ROHMUSDC/ROHMSensorPlatformEVK/Documentation/CE Declaration of Conformity/EUDC-DoC-201501-SENSEKIT2-EVK-101.pdf

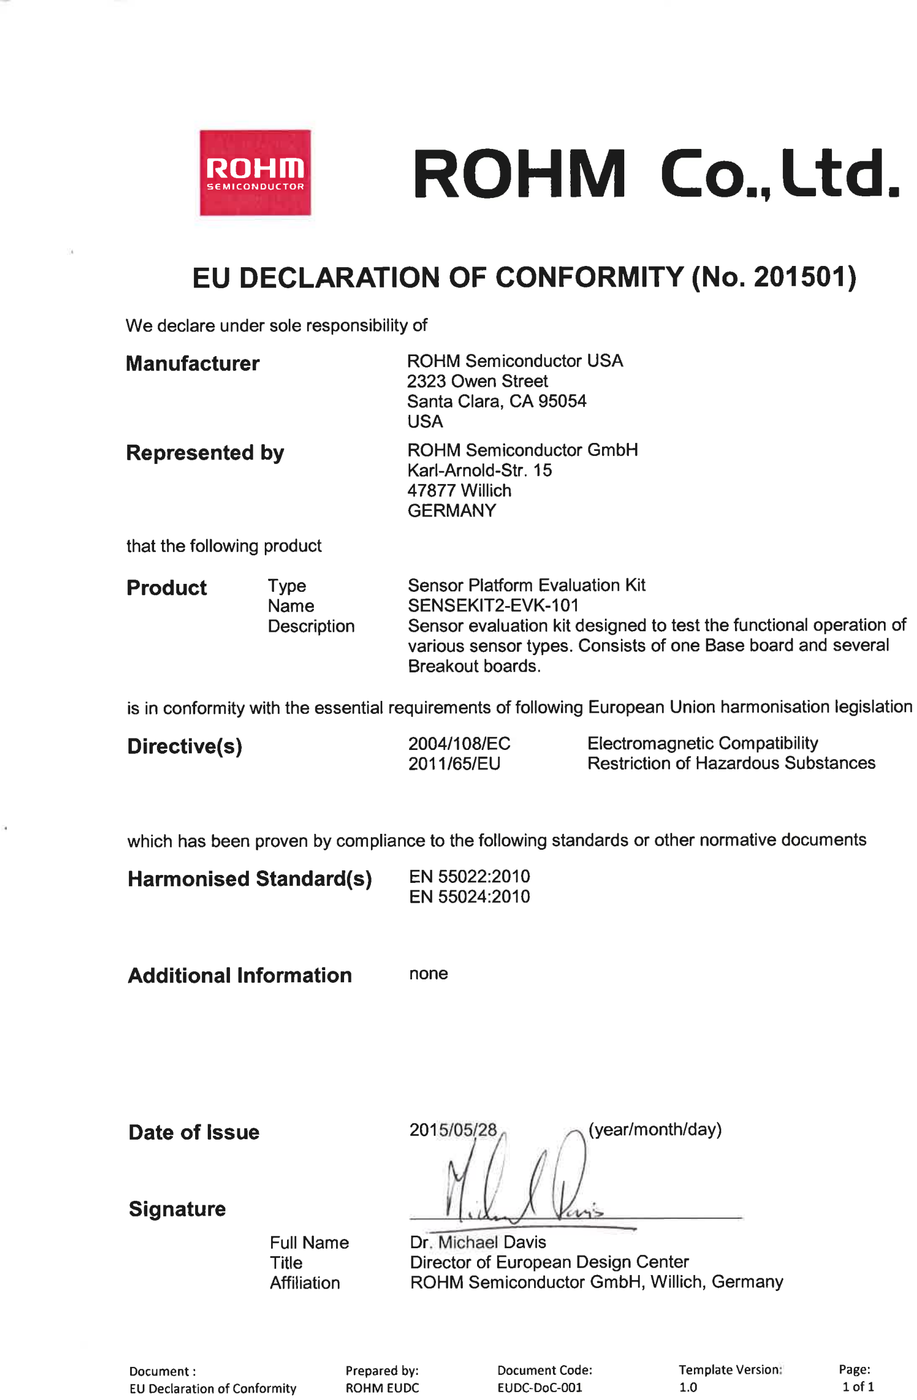
[picture p3: page 1]
