ROHMUSDC/ROHMSensorPlatformEVK/Documentation/CE Declaration of Conformity/technical_documentation/[14]_Photos/IMG_20150430_091738.jpg

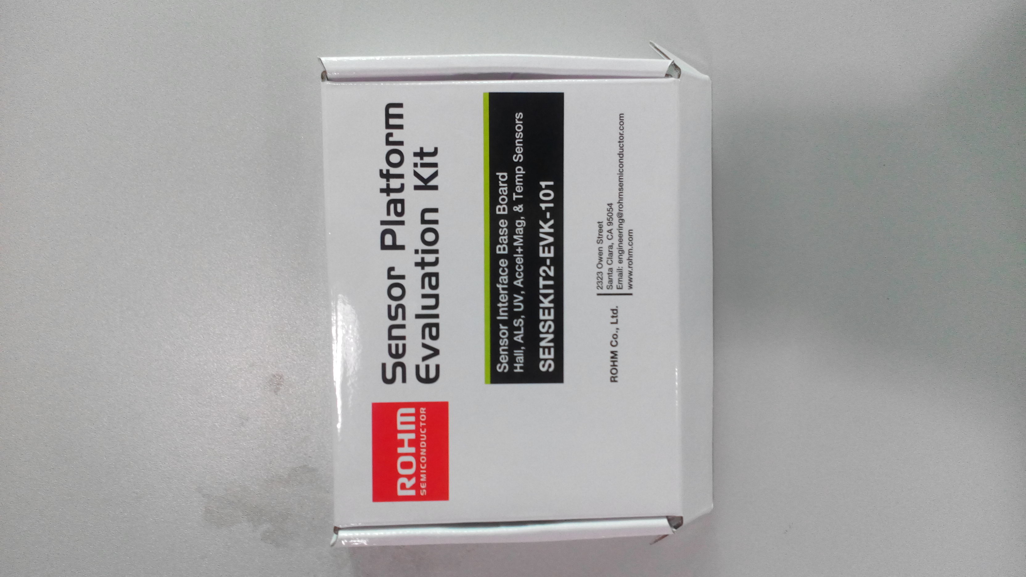
Documentation/CE Declaration of Conformity/technical_documentation/[14]_Photos/IMG_20150430_091738.jpg
