ROHMUSDC/ROHMSensorPlatformEVK/Documentation/CE Declaration of Conformity/technical_documentation/[14]_Photos/IMG_20150430_091749.jpg

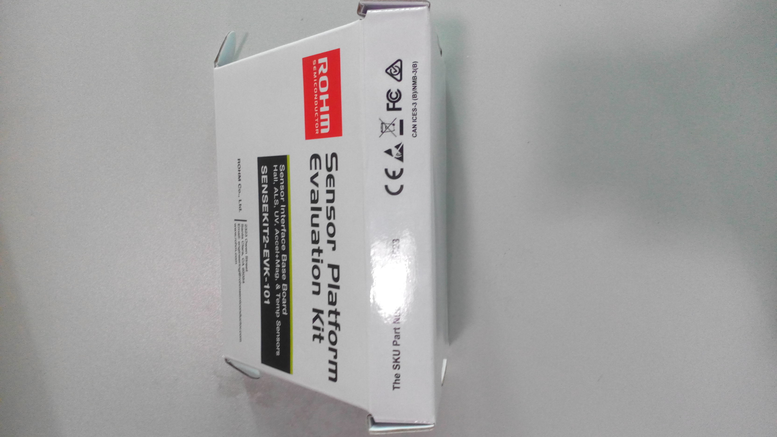
Documentation/CE Declaration of Conformity/technical_documentation/[14]_Photos/IMG_20150430_091749.jpg
