ROHMUSDC/ROHMSensorPlatformEVK/Documentation/CE Declaration of Conformity/technical_documentation/[6]_Rohm Sensor Kit BOM - 20150610 (6010428).pdf

BOM

6010428 ROHM Sensor EVK ROHM Sensor EVK

No. | P/N | Name | Spec. | Usage | Location | Manufacturer | Description | Package | Document
.1 | 1106001000109 | Carton | Carton 475*475*405mm,K=K | 0.0056 | | | 纸箱,外尺寸475*475*405mm,K=K
.1 | 1106001000165 1106002000041 | Color gift box ANTI-STATIC BAG | ROHM_Sensor_EVK_BOX_REV1.0_142*113* ANTI-STATIC BAG,150*110mm 24mm | 1 1.0000 | seal with plastic-envelop machine | AVL JIDA | ROHM_Sensor_EVK_BOX_REV1.0_142*113* Anti-static bag,150*110mm 24mm | - .1
.1 | 1106002000081 | FOAM | ROHM_Sensor_EVK_Foam_REV1.0,115*55* 15mm,slot:80*25*10mm | 1.0000 | | . | ROHM_Sensor_EVK_Foam_REV1.0,115*55*1 5mm,slot:80*25*10mm | -
.1 | 1106003000294 | Quick Start Guide | ROHM_Sensor_EVK_QSG_REV1.0_130*100 mm,128 gsm bond paper | 1 | | . | ROHM_Sensor_EVK_QSG_REV1.0_130*100 mm,128 gsm bond paper | Bulk
.1 | 1106003000295 | Safety Instructions | _REV1.0_130*100mm,100 gsm uncoated paper | 1 | | . | _REV1.0_130*100mm,100 gsm uncoated paper | Bulk
.1 | 400665 | ROHM_SENSOR_PLATFORM_BASE_BOARD_BOM_REV02 PCBA | ROHM_SENSOR_PLATFORM_BASE_BOAR D_BOM_REV02 PCBA | 1 | | Embest | ROHM_SENSOR_PLATFORM_BASE_BOAR D_BOM_REV02 PCBA | -
..2 | 1001001000386 | PCB | ROHM_SENSOR_PLATFORM_BASE_BOAR D_REV02 PCB | 1 | PCB | AVL | 2 layers PCB,Green Soldermask,white Silkscreen,Immersiongold,65X25mm,ROHM_S ENSOR_PLATFORM_BASE_BOARD_REV02 | - | Rohm PCB.pdf, 2014 Flux.PDF, 2015 Flux.PDF, 2015 SnCu.PDF, 2015 Solder.PDF, 2015 Solution 2.PDF, 2015 Solution.PDF
..2 | 1002002100162C | MCU | ML610Q112-NNNTCZ07FL | 1 | U4 | Rohm | 32LQFP,ML610Q112-NNNTCZ07FL,Rohm,customer supply | 32LQFP | http://www.rohm.com/web/global/rohs-compliance-information
..2 | 1002006100152C | LDO | BU33TD3WG-TR | 1 | U1 | ROHM | IC REG LDO 3.3V 0.2A SSOP5,BU33TD3WG-TR,Rohm,customer supply | SSOP5 | http://www.rohm.com/web/global/rohs-compliance-information
..2 | 1002010100072 | Interface | FT230XS-R | 1 | U70 | FTDI | IC,FT230X USB TO BASIC UART IC,FT230XS-R,SSOP-16,SMD | SSOP-16 | Rohs Statement Devices QD_104.pdf
..2 | 1003001100687C | Thick film Resistor | MCR01MRTF1002 | 11 | R1,R3,R6,R7,R36,R149,R150,R151,R152,R153,R154 | Rohm | SMD,MCR01MRTF1002,Rohm,customer supply | 0402 | http://www.rohm.com/web/global/rohs-compliance-information
..2 | 1003001100688C | Thick film Resistor | MCR03ERTJ000 | 2 | R2,R5 | Rohm | RES 0.0 OHM 1/10W JUMP 0603 SMD,MCR03ERTJ000,Rohm,customer supply | 0603 | http://www.rohm.com/web/global/rohs-compliance-information
..2 | 1003001100689C | Thick film Resistor | MCR01MRTF2002 | 1 | R4 | Rohm | SMD,MCR01MRTF2002,Rohm,customer supply | 0402 | http://www.rohm.com/web/global/rohs-compliance-information
..2 | 1003001100690C | Thick film Resistor | MCR01MRTF1501 | 8 | R14,R15,R16,R17,R18,R19,R20,R21 | Rohm | SMD,MCR01MRTF1501,Rohm,customer supply | 0402 | http://www.rohm.com/web/global/rohs-compliance-information
..2 | 1003001100691C | Thick film Resistor | MCR01MRTJ271 | 2 | R37,R38 | Rohm | RES 270 OHM 1/16W 5% 0402 SMD,MCR01MRTJ271,Rohm,customer supply | 0402 | http://www.rohm.com/web/global/rohs-compliance-information
..2 | 1003001100692C | Thick film Resistor | MCR01MRTJ270 | 2 | R39,R40 | Rohm | RES 27 OHM 1/16W 5% 0402 SMD,MCR01MRTJ270,Rohm,customer supply | 0402 | http://www.rohm.com/web/global/rohs-compliance-information
..2 | 1003001100693C | Thick film Resistor | MCR01MRTF1502 | 1 | R41 | Rohm | SMD,MCR01MRTF1502,Rohm,customer supply | 0402 | http://www.rohm.com/web/global/rohs-compliance-information
..2 | 1003001100694C | Thick film Resistor | TRR01MZPF2400 | 2 | R155,R156 | Rohm | SMD,TRR01MZPF2400,Rohm,customer supply | 0402 | http://www.rohm.com/web/global/rohs-compliance-information
..2 | 1004001100038 | Ceramic Capacitor | GRM155R71E103KA01D | 3 | C4,C30,C33 | Murata | CAP,10NF,+/-10%,X7R,25V,SMD0402 | 0402 | Murata_CO2E_100112-558472.pdf
..2 | 1004001100053 | Ceramic Capacitor | GRM155R61A474KE15D | 2 | C1,C3 | Murata | CAP,470NF,+/-10%,X5R,10V,SMD0402 | 0402 | Murata_CO2E_100112-558472.pdf
..2 | 1004001100187 | Ceramic Capacitor | GRM155R61A104KA01D | 3 | C28,C29,C34 | Murata | CAP,100NF,+/-10%,X5R,10V,SMD0402 | 0402 | Murata_CO2E_100112-558472.pdf
..2 | 1004001100218 | Ceramic Capacitor | GRM155R60J475ME47 | 1 | C5 | Murata | CAP,4.7UF,+/-20%,X5R,6.3V,SMD0402 | 0402 | Murata_CO2E_100112-558472.pdf
..2 | 1004001100310 | Ceramic Capacitor | GRM1555C1H470FA01D | 2 | C31,C32 | Murata | CAP CER 47PF 50V 1% NP0 0402,GRM1555C1H470FA01D,murata | 0402 | Murata_CO2E_100112-558472.pdf
..2 | 1004004100058 | Aluminum Electrolytic CapacitorUUT1E4R7MCL1GS | | 1 | C27 | Nichicon | CAP ALUM 4.7UF 25V 20% SMD,UUT1E4R7MCL1GS,Nichicon | SMD | e-ut.pdf
..2 | 1005005100063 | Ferrite Bead | MI0603J601R-10 | 1 | FB1 | Laird-Signal | FERRITE CHIP POWER 600 OHM SMD,MI0603J601R-10,Laird-Signal Integrity Products | 0603 | MI0603J601R-10.pdf
..2 | 1006001100066C | LED | SML-P11VTT86 | 8 | D8,D9,D10,D11,D12,D13,D14,D15 | ROHM | LED 0402 RED 50MW 20MA SMD,SML-P11VTT86,Rohm,customer supply | 0402 | http://www.rohm.com/web/global/rohs-compliance-information
..2 | 1006001100067C | LED | SML-P24MUWT86 | 1 | D16 | ROHM | LED PICOLED DUAL WGN/RED 1010,SML-P24MUWT86,Rohm,customer supply | 1010 | http://www.rohm.com/web/global/rohs-compliance-information
..2 | 1006001100069C | LED | SML-210MTT86 | 1 | LED1 | ROHM | LED 570NM GREEN WTR CLR 0805 SMD,SML-210MTT86,Rohm,customer supply | 0805 | http://www.rohm.com/web/global/rohs-compliance-information
..2 | 1006001100070C | LED | SML-210YTT86 | 1 | LED2 | ROHM | LED 585NM YLW WTR CLR 0805 SMD,SML-210YTT86,Rohm,customer supply | 0805 | http://www.rohm.com/web/global/rohs-compliance-information
..2 | 1006002100064C | Diode | RB051M-2YTR | 1 | D1 | ROHM | DIODE SCHOTTKY 20V 3A PMDU,RB051M-2YTR,Rohm，customer supply | SOD-123 | http://www.rohm.com/web/global/rohs-compliance-information
..2 | 1009001200003 | Pin Header | P6E02A-602530-B1 | 1 | J3 | CHIN-BAN | Connector,Pin Header,Straight,Male,1x2Pin,2.54MM pitch,6.00,3.00,Gold Flash 1u, black,DIP | DIP | CHIN-BAN (C2680(MJ501-E0GF-B-K).PDF, CHIN-BAN (P10-2x02SGF-116A-NG).pdf, CHIN-BAN (PA6T EN430 BK(P10-2x02SGF-116A-NG).pdf, CHIN-BAN (PBT BK&NA(P101-1x05SGF-116A-NX).PDF
..2 | 1009001200009 | Pin Header | P6E03A-602530-B1 | 1 | J2 | CHIN-BAN | Connector,Pin Header,Straight,Male,1x3Pin,2.54MM pitch,6.00,3.00,Gold Flash 1u, black,DIP | DIP | CHIN-BAN (C2680(MJ501-E0GF-B-K).PDF, CHIN-BAN (P10-2x02SGF-116A-NG).pdf, CHIN-BAN (PA6T EN430 BK(P10-2x02SGF-116A-NG).pdf, CHIN-BAN (PBT BK&NA(P101-1x05SGF-116A-NX).PDF
..2 | 1009001200013 | Pin Header | P101-2*02SGF-116A-NX | 1 | J4 | Townes | Connector,Pin Header,Straight,Male,2x2Pin,2.54MM pitch,6.06,3.00,Gold Flash 1u, black,DIP | DIP | Townes (MJ501-E0GF-B-K).pdf, Townes (P10-2x02SGF-116A-NG.PDF, Townes (P101-1x05SGF-116A-NX).pdf, Townes (P101-2x02SGF-116A-NX).PDF

BOM

..2 | 1009002200122 | Pin Socket | 960105-6202-AR | 2 | U2,U3 | 3M | CONN SOCKET SGL VERT 1*5POS,7.1/3.0,960105-6202-AR,3M | DIP | 3M-960108-6202-AR-datasheet.pdf
..2 | 1009002200123 | Pin Socket | 960106-6202-AR | 1 | U5 | 3M | CONN SOCKET SGL VERT 1*6POS,7.1/3.0,960106-6202-AR,3M | DIP | 3M-960108-6202-AR-datasheet.pdf
..2 | 1009007100054 | USB Connector | 480372200 | 1 | J8 | molex | CONN PLUG USB A 4POS SMD R/A,480372200,Molex | SMD | 0480372200_rohs.pdf
..2 | 1009016000005 | Shunt | MJ501-EOGF-B-K | 1.00 | Shunt | Townes | Connector,Shunt,2Pin,2.54MM Pitch,6MM Height,Gold Flash 1u,black | | Townes (MJ501-E0GF-B-K).pdf, Townes (P10-2x02SGF-116A-NG.PDF, Townes (P101-1x05SGF-116A-NX).pdf, Townes (P101-2x02SGF-116A-NX).PDF
..2 | 1010001200015 | Tacticle Switch | FSM4JH | 1 | S1 | Tyco | Switch,Tacticle,160gf,black housing,black plunger, 6*6*5MM,DIP | DIP | ENG_PC_MD_1825910-6_A.pdf
..2 | 1010004200018 | Slide Switch | MHS123 | 1 | J1 | Apem | 30V,MHS123,Apem | DIP | Apem ROHS.pdf
.1 | 400666 | ROHM_SENSOR_PLATFORM_BREAKOUT_BOARD_BOM_6BoardsOnly_ | ROHM_SENSOR_PLATFORM_BREAKOUT_ BOARD_BOM_6BoardsOnly_REV02 | 1 | | Embest | ROHM_SENSOR_PLATFORM_BREAKOUT_ BOARD_BOM_6BoardsOnly_REV02 | -
..2 | 1001001000385 | PCB | ROHM_SENSOR_PLATFORM_BREAKOUT_ BOARD_REV02 PCB | 1 | PCB | AVL | Silkscreen,Immersiongold,60X55mm,ROHM_S ENSOR_PLATFORM_BREAKOUT_BOARD_ REV02 | - | Rohm PCB.pdf, 2014 Flux.PDF, 2015 Flux.PDF, 2015 SnCu.PDF, 2015 Solder.PDF, 2015 Solution 2.PDF, 2015 Solution.PDF
..2 | 1002021100054C | Sensor | BH1721FVC-TR | 1 | U13 | Rohm | IC AMBIENT LIGHT SENSOR WSOF5,Digital 16bit serial output type | WSOF5 | http://www.rohm.com/web/global/rohs-compliance-information
..2 | 1002021100055C | Sensor | BH1620FVC-TR | 1 | U10 | Rohm | IC AMBIENT LIGHT SENSOR WSOF5,Analog current output type | WSOF5 | http://www.rohm.com/web/global/rohs-compliance-information
..2 | 1002021100056C | Sensor | BDE0600G-TR | 1 | U51 | Rohm | IC TEMP SENSOR THERM 60°C SSOP5 | SSOP5 | http://www.rohm.com/web/global/rohs-compliance-information
..2 | 1002021100057C | Sensor | ML8511-00FCZ05B | 1 | U59 | Rohm | UV SENSOR W/AMP TQFN12 | TQFN12 | http://www.rohm.com/web/global/rohs-compliance-information
..2 | 1002021100058C | Sensor | KMX61 | 1 | U66 | Rohm | MAGNETOMETER AND ACCELEROMETER TRI-AXIS LGA16 | LGA16 | http://www.rohm.com/web/global/rohs-compliance-information
..2 | 1002021100059C | Sensor | BU52011HFV-TR | 1 | U110 | Rohm | IC HALL EFFECT SW BIPO HVSOF5,Omnipolar Detection | HVSOF5 | http://www.rohm.com/web/global/rohs-compliance-information
..2 | 1003001100687C | Thick film Resistor | MCR01MRTF1002 | 1 | R32 | Rohm | SMD,MCR01MRTF1002,Rohm,customer supply | 0402 | http://www.rohm.com/web/global/rohs-compliance-information
..2 | 1003001100688C | Thick film Resistor | MCR03ERTJ000 | 11 | R130,R162,R167,R169,R188,R198,R200,R213,R234,R235,RRohm | | RES 0.0 OHM 1/10W JUMP 0603 SMD,MCR03ERTJ000,Rohm,customer supply | 0603 | http://www.rohm.com/web/global/rohs-compliance-information
..2 | 1003001100695C | Thick film Resistor | MCR01MRTF1001 | 1 | R22 | Rohm | RES 1K OHM 1/16W 1% 0402 SMD,customer supply | 0402 | http://www.rohm.com/web/global/rohs-compliance-information
..2 | 1003001100696C | Thick film Resistor | MCR03ERTF4701 | 1 | R129 | Rohm | RES 4.7K OHM 1/10W 1% 0603 SMD,customer supply | 0603 | http://www.rohm.com/web/global/rohs-compliance-information
..2 | 1003001100697C | Thick film Resistor | TRR01MZPF5601 | 1 | R132 | Rohm | RES 5.6K OHM 1/16W 1% 0402 SMD,customer supply | 0402 | http://www.rohm.com/web/global/rohs-compliance-information
..2 | 1004001100030 | Ceramic Capacitor | GRM155R71H102KA01D | 1 | C21 | Murata | CAP,1NF,+/-10%,X7R,50V,SMD0402 | 0402 | Murata_CO2E_100112-558472.pdf
..2 | 1004001100056 | Ceramic Capacitor | GRM155R60J105KE19D | 2 | C9,C24 | Murata | CAP,1UF,+/-10%,X5R,6.3V,SMD0402 | 0402 | Murata_CO2E_100112-558472.pdf
..2 | 1004001100162 | Ceramic Capacitor | GRM21BR60J226ME39L | 1 | C78 | Murata | CAP,22UF,+/-20%,X5R,6.3V,SMD0805 | 0805 | Murata_CO2E_100112-558472.pdf
..2 | 1004001100187 | Ceramic Capacitor | GRM155R61A104KA01D | 7 | C6,C7,C20,C22,C23,C35,C50 | Murata | CAP,100NF,+/-10%,X5R,10V,SMD0402 | 0402 | Murata_CO2E_100112-558472.pdf
..2 | 1009001200009 | Pin Header | P6E03A-602530-B1 | 2 | J6,J7 | CHIN-BAN | Connector,Pin Header,Straight,Male,1x3Pin,2.54MM pitch,6.00,3.00,Gold Flash 1u, black,DIP | DIP | CHIN-BAN (C2680(MJ501-E0GF-B-K).PDF, CHIN-BAN (P10-2x02SGF-116A-NG).pdf, CHIN-BAN (PA6T EN430 BK(P10-2x02SGF-116A-NG).pdf, CHIN-BAN (PBT BK&NA(P101-1x05SGF-116A-NX).PDF
..2 | 1009001200016 | Pin Header | P101-1*05SGF-116A-NX | 12 | U9,U12,U50,U58,U65,U111,U11,U14,U46,U60,U67,U113 | Townes | Connector,Pin Header,Straight,Male,1x5Pin,2.54MM pitch,6.06,3.00,Gold Flash 1u, black,DIP | DIP | Townes (MJ501-E0GF-B-K).pdf, Townes (P10-2x02SGF-116A-NG.PDF, Townes (P101-1x05SGF-116A-NX).pdf, Townes (P101-2x02SGF-116A-NX).PDF
..2 | 1009001200108 | Pin Header | P6E06A-602530-B1 | 6 | U16,U17,U69,U52,U61,U112 | CHIN-BAN | Connector,Pin Header,Straight,Male,1x6Pin,2.54MM pitch,6.00,3.00,Gold Flash 1u, black,DIP | DIP | CHIN-BAN (C2680(MJ501-E0GF-B-K).PDF, CHIN-BAN (P10-2x02SGF-116A-NG).pdf, CHIN-BAN (PA6T EN430 BK(P10-2x02SGF-116A-NG).pdf, CHIN-BAN (PBT BK&NA(P101-1x05SGF-116A-NX).PDF
..2 | 1009016000005 | Shunt | MJ501-EOGF-B-K | 2.00 | Shunt | Townes | Connector,Shunt,2Pin,2.54MM Pitch,6MM Height,Gold Flash 1u,black | | Townes (MJ501-E0GF-B-K).pdf, Townes (P10-2x02SGF-116A-NG.PDF, Townes (P101-1x05SGF-116A-NX).pdf, Townes (P101-2x02SGF-116A-NX).PDF
