ROHMUSDC/ROHMSensorPlatformEVK/Documentation/CE Declaration of Conformity/technical_documentation/[3]_ROHM_SENSOR_PLATFORM_SCHEMATIC_20140918.pdf

REM Control Switches, Fixed Headers, 2014-07-21; Page; Contents; Table of Contents/Revision History; Sensor Platform Base Board; FTDI Details; Rev; Initial release 2014-07-17

- Add hierachical port REG_OUT into FTDI block.
- Add dual LED D16.

Title
Sensor Platform Schematic

Size Size Size B | Document Number Document Number Document Number Table of Contents/Revision History Table of Contents/Revision History Table of Contents/Revision History | Rev Rev Rev 02 02 02

Date: Wednesday, September 17, 2014 Wednesday, September 17, 2014 Wednesday, September 17, 2014 | Sheet 1 1 1 of 3 3 3

# INPUT POWER

# RESET MCUs


>> Coin Cell does not need to be
On-Board. We would like to have
the positive and GND leads on a 2
position header (J1)

>> 3 Position Switch (J15)
Case 1: Middle pin OPEN
Case 2: Middle pin con to VBUS
Case 3: Middle pin con to Ext. Power

>> 5V @ Vbus when USB is connected.
If this is connected, 5V is divided down
to 3V and connected MCU. MCU pin

Sensor Breakout Board Interface
>> All headers are female types.

>> This should be a standard pitch 2x2
pin male header. This is a depreceated
version of the debugger/programmer port.
Need to build an interface cable to use
our original cable
Extra Header Rows

» This does not need to be populated on a
8x2 header. These can really just be VIAS
at a standard pitch. Single or Double row
is OK depending on the base board module
size.

Standalone Mode LED Feedback Section

» See Page 3 for full
details of this block

Title
Sensor Platform - Base Board

>> Using ROHM Red PicoLEDs

Size Size Size | Document Number Document Number Document Number Sensor Platform - Base Board Schematic Sensor Platform - Base Board Schematic Sensor Platform - Base Board Schematic | Rev Rev Rev 02 02 02

Thursday, September 18, 2014 Thursday, September 18, 2014 Thursday, September 18, 2014 | 2 2 2 3 3 3

# USB to serial UART interface


3 | USBDP 8
4 | | RST 11

The MTP memory on this FT-230XS-R device can
be programmed directly over USB, using the
FT_Prog utility to set the required options
and program it. See:
www.ftdichip.com/Support/Utilities.htm#FT_Prog

Title
Sensor Platform - Base Board FTDI IC

Size Size Size | Document Number Document Number Document Number FTDI Portion of Circuit FTDI Portion of Circuit FTDI Portion of Circuit | Rev Rev Rev 02 02 02

Thursday, September 18, 2014 Thursday, September 18, 2014 Thursday, September 18, 2014 | 3 3 3

# ROHM Sensor Platform Breakout Boards

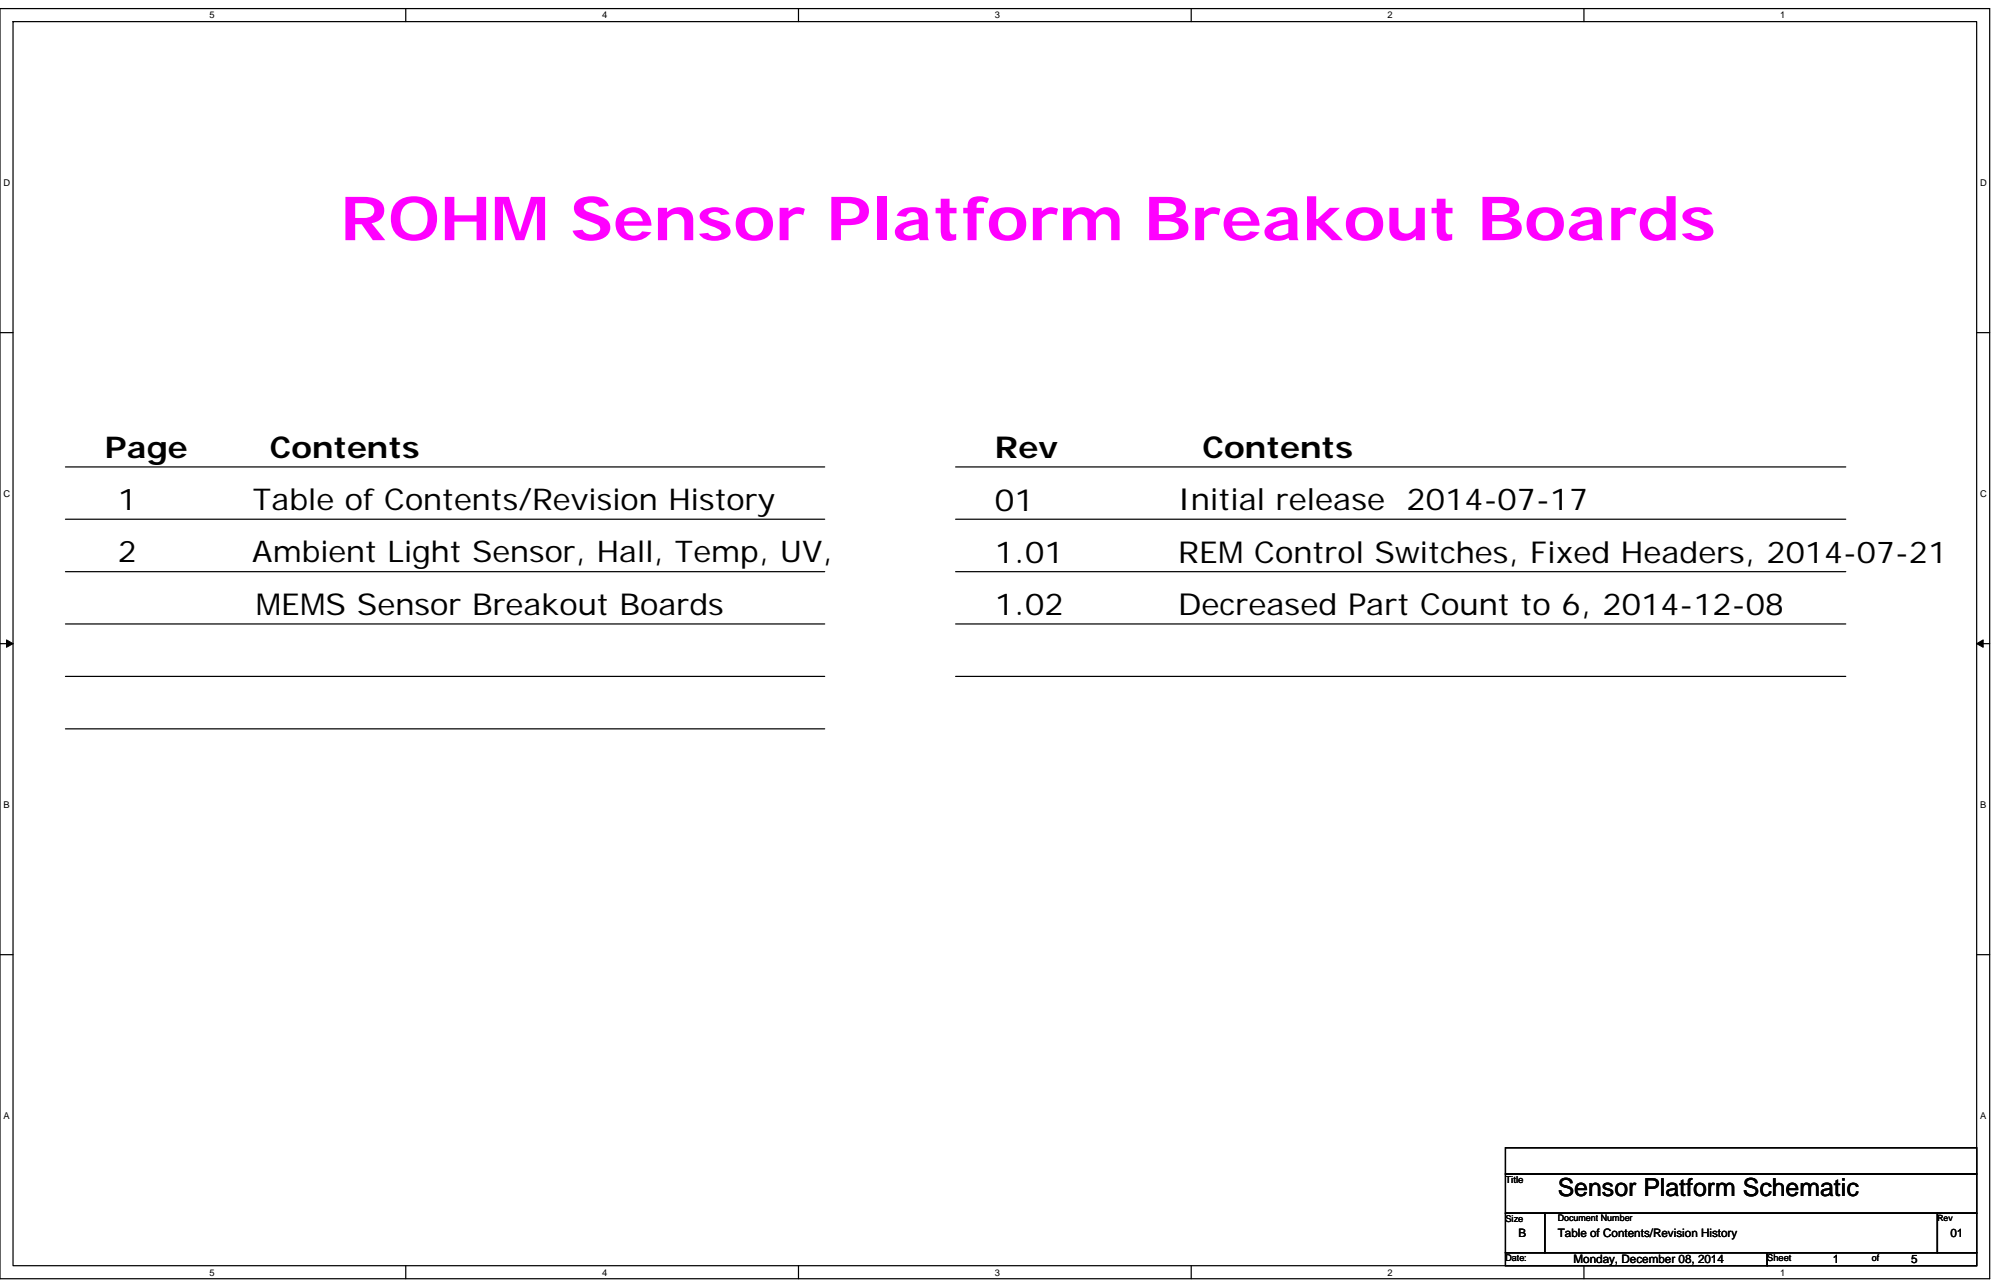
[picture p64: page 4]
REM Control Switches, Fixed Headers, 2014-07-21; Page; Contents; Table of Contents/Revision History; Rev; Initial release 2014-07-17; Ambient Light Sensor, Hall, Temp, UV,; Decreased Part Count to 6, 2014-12-08; Title

MEMS Sensor Breakout Boards

Sensor Platform Schematic

Size Size Size B B B | Document Number Document Number Document Number Table of Contents/Revision History Table of Contents/Revision History Table of Contents/Revision History | Rev Rev Rev 01 01 01

Date: Date: Date: Monday, December 08, 2014 Monday, December 08, 2014 Monday, December 08, 2014 | Sheet Sheet Sheet 1 1 1 of of of 5 5 5

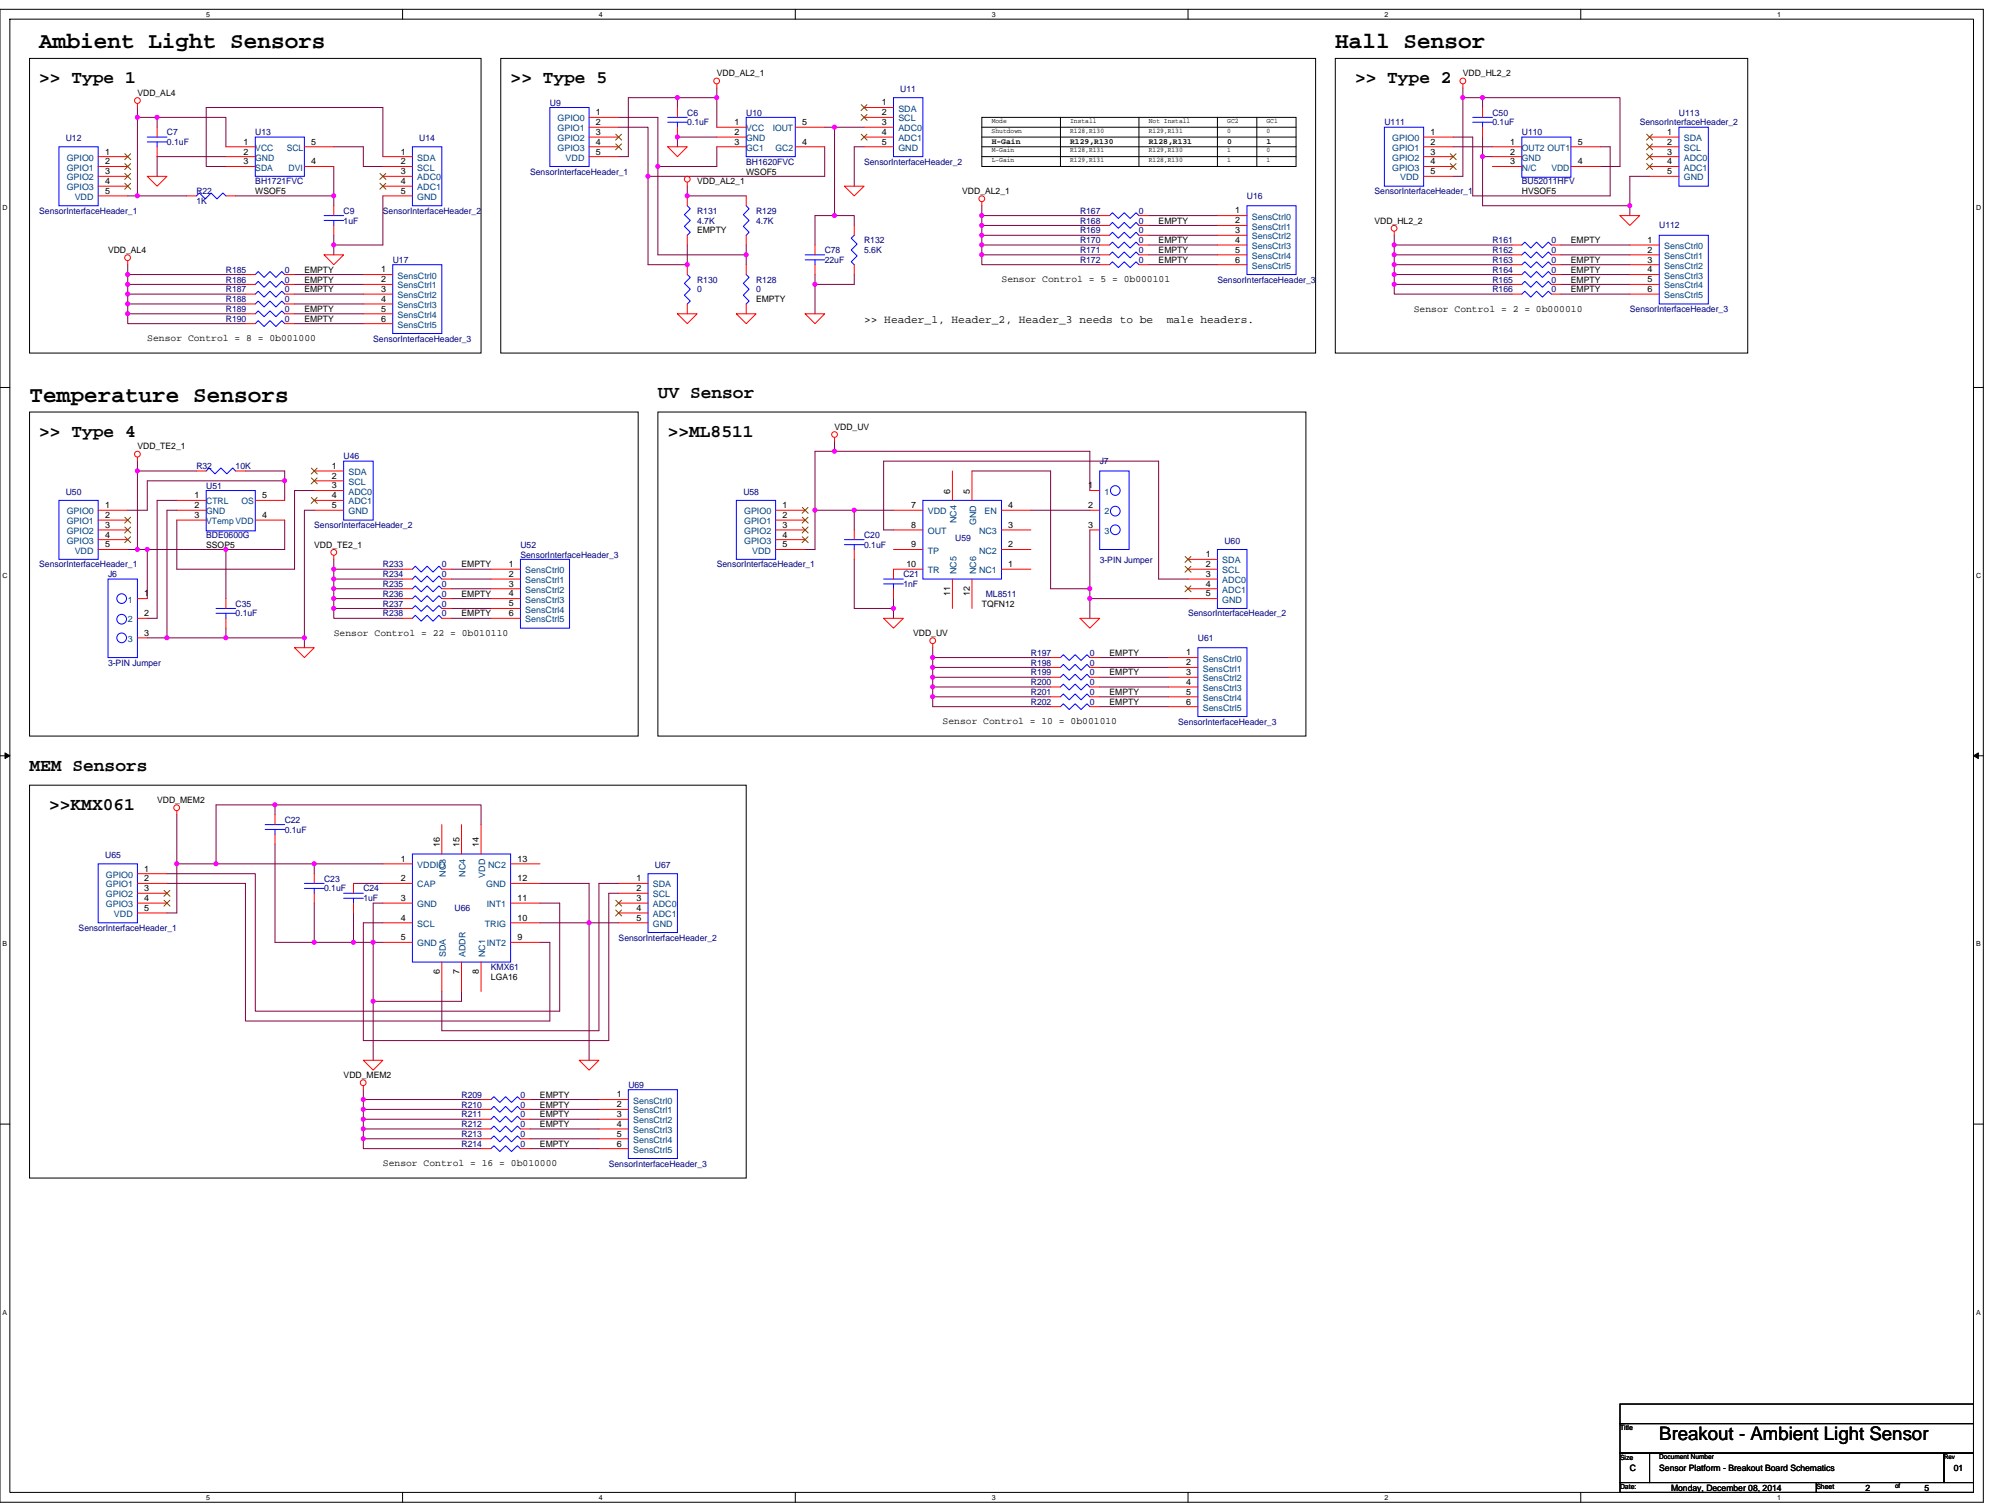
[picture p65: page 5]

>> Header_1, Header_2, Header_3 needs to be male headers.

Breakout - Ambient Light Sensor
