ROHMUSDC/ROHMSensorPlatformEVK/Documentation/CE Declaration of Conformity/technical_documentation/[7]_Rohm Sensor Kit BOM Details/MI0603J601R-10.pdf

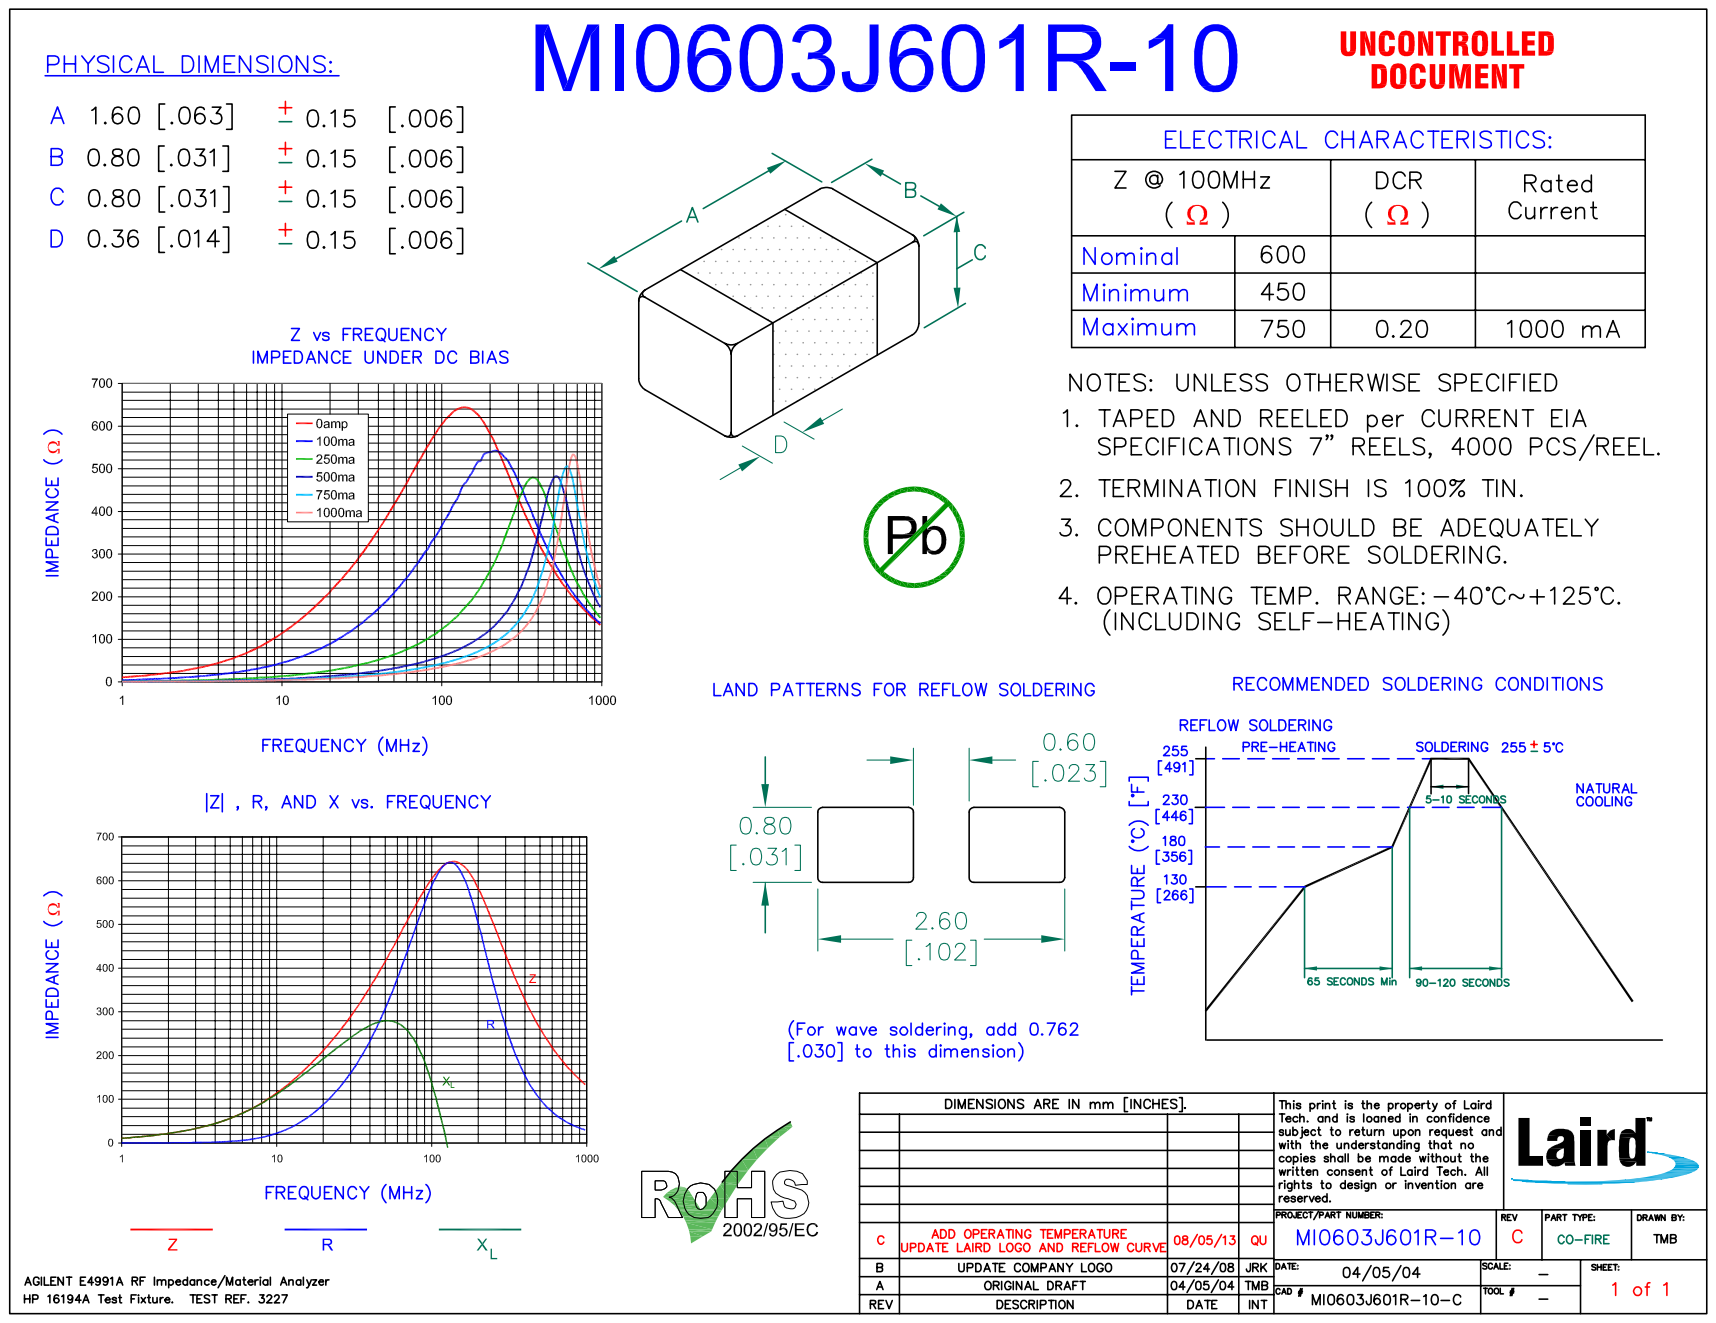
[picture p69: page 1]
