ROHMUSDC/ROHMSensorPlatformEVK/Documentation/CE Declaration of Conformity/technical_documentation/[13]_Giftbox Ver.02.pdf

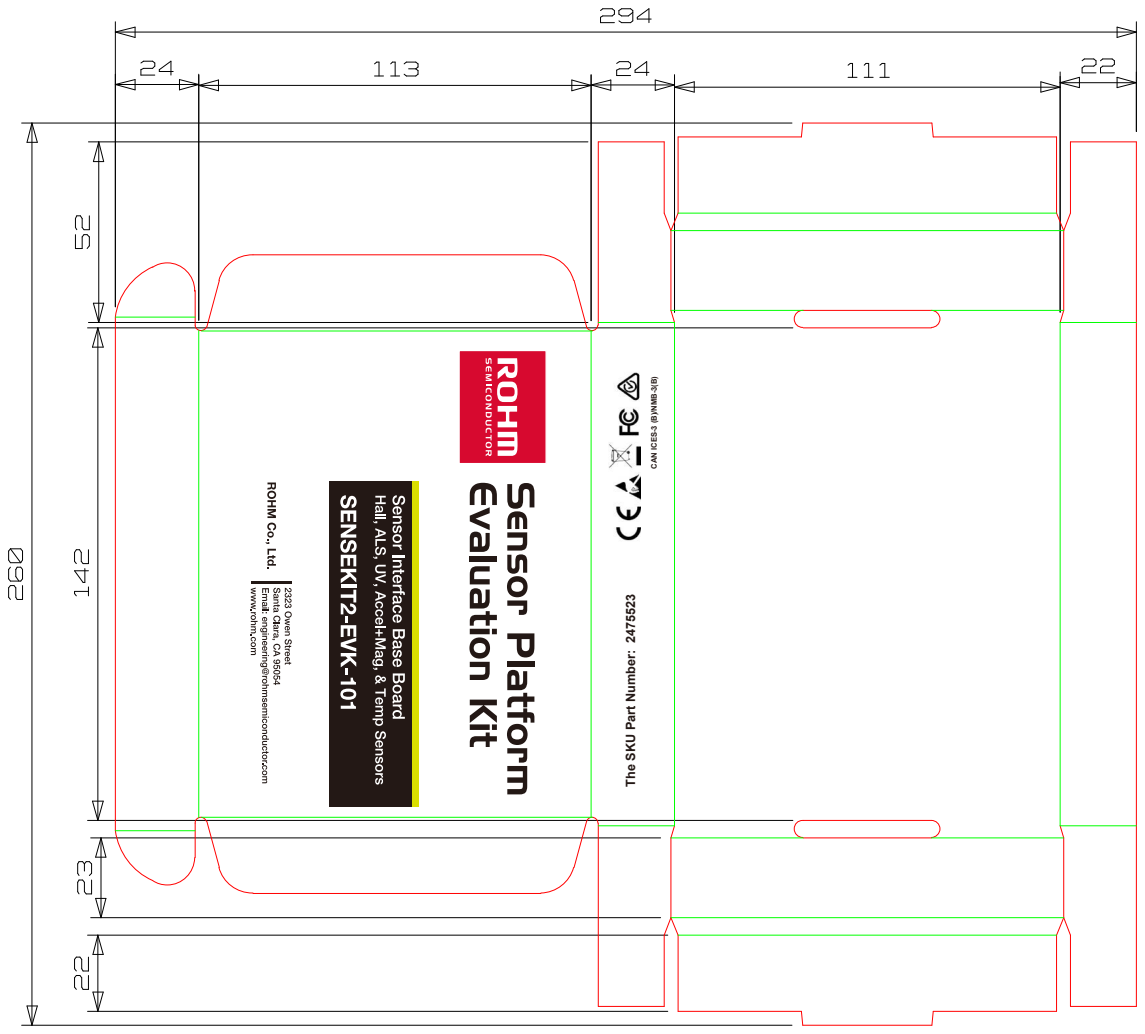
[picture p70: page 1]

CAN ICES-3 (B)/NMB-3(B)

The SKU Part Number: 2475523
