ROHMUSDC/ROHMSensorPlatformEVK/Documentation/CE Declaration of Conformity/technical_documentation/[5]_BreakoutBoard_Layout_20150803.pdf

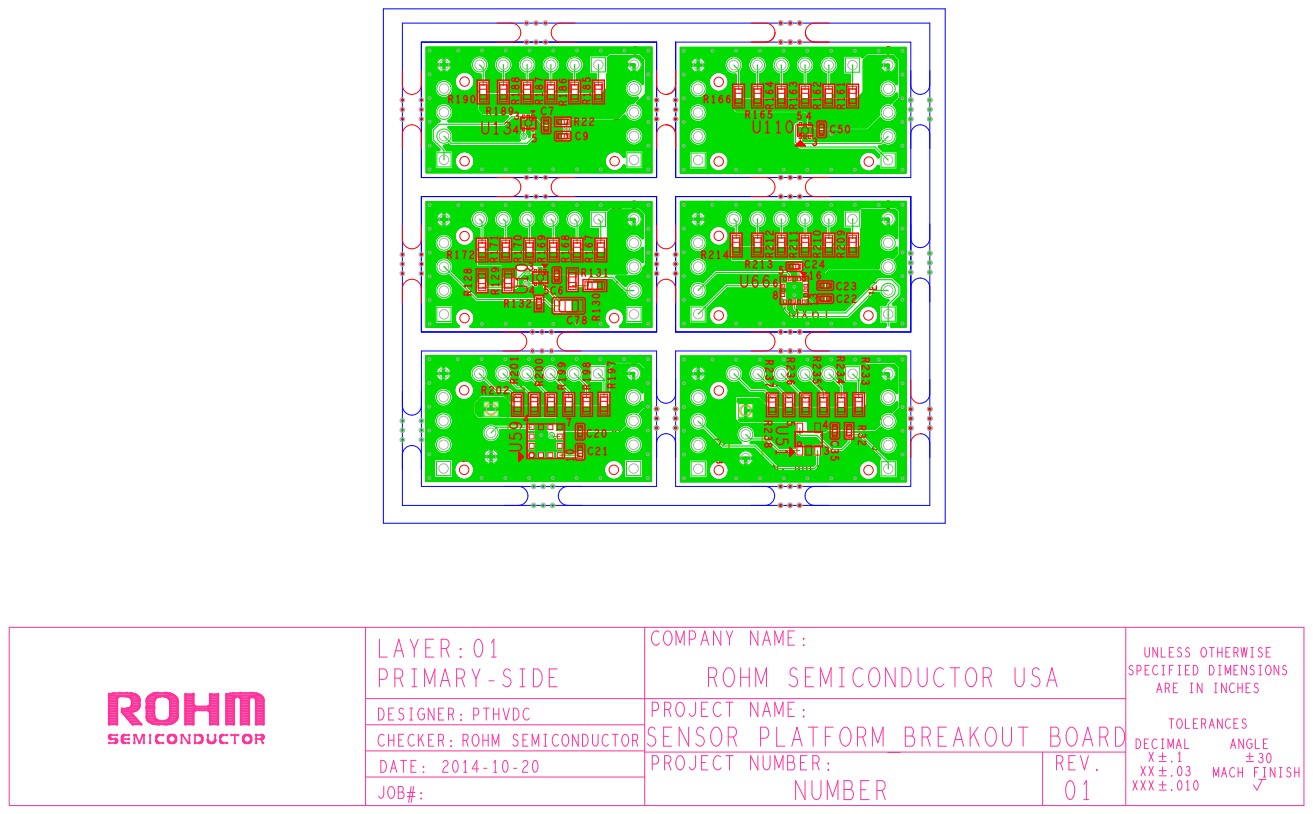
[picture p71: page 1]

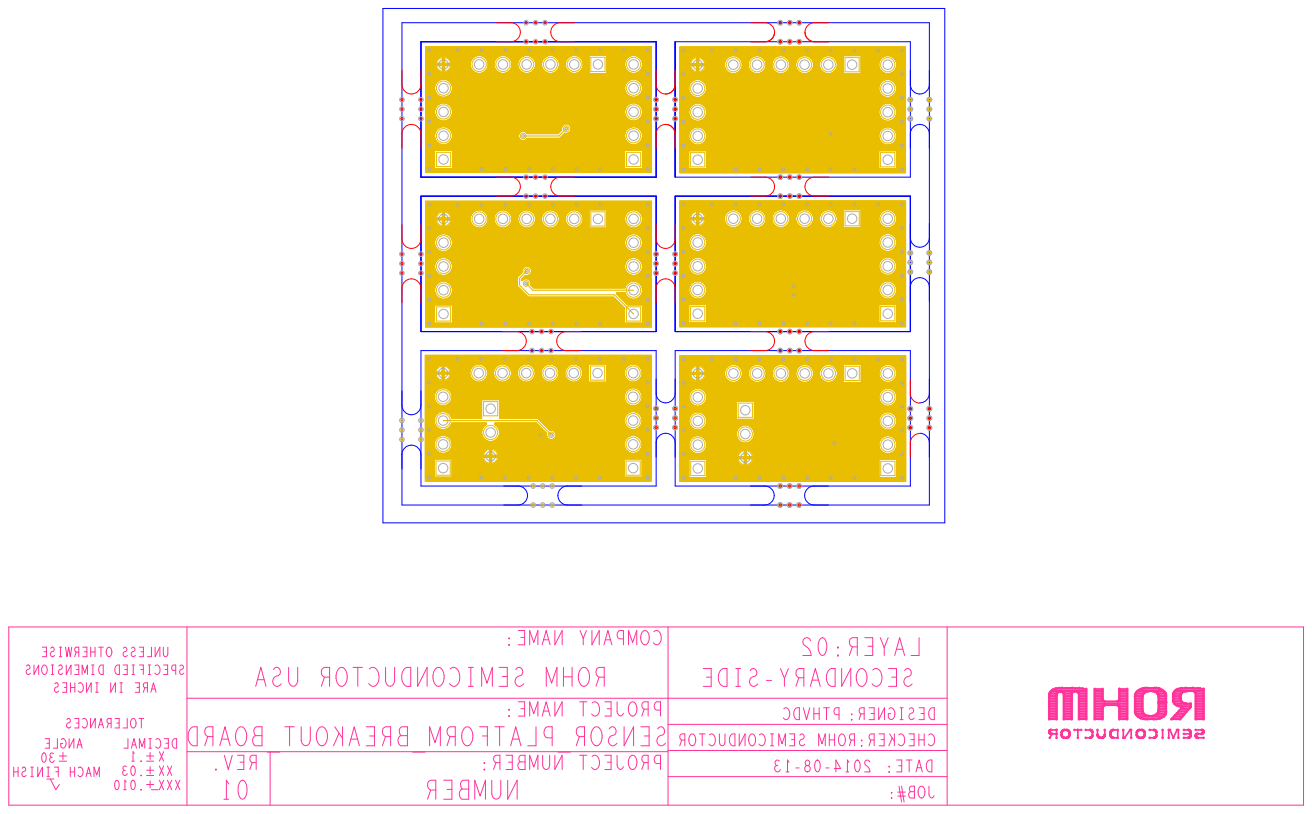
[picture p72: page 2]

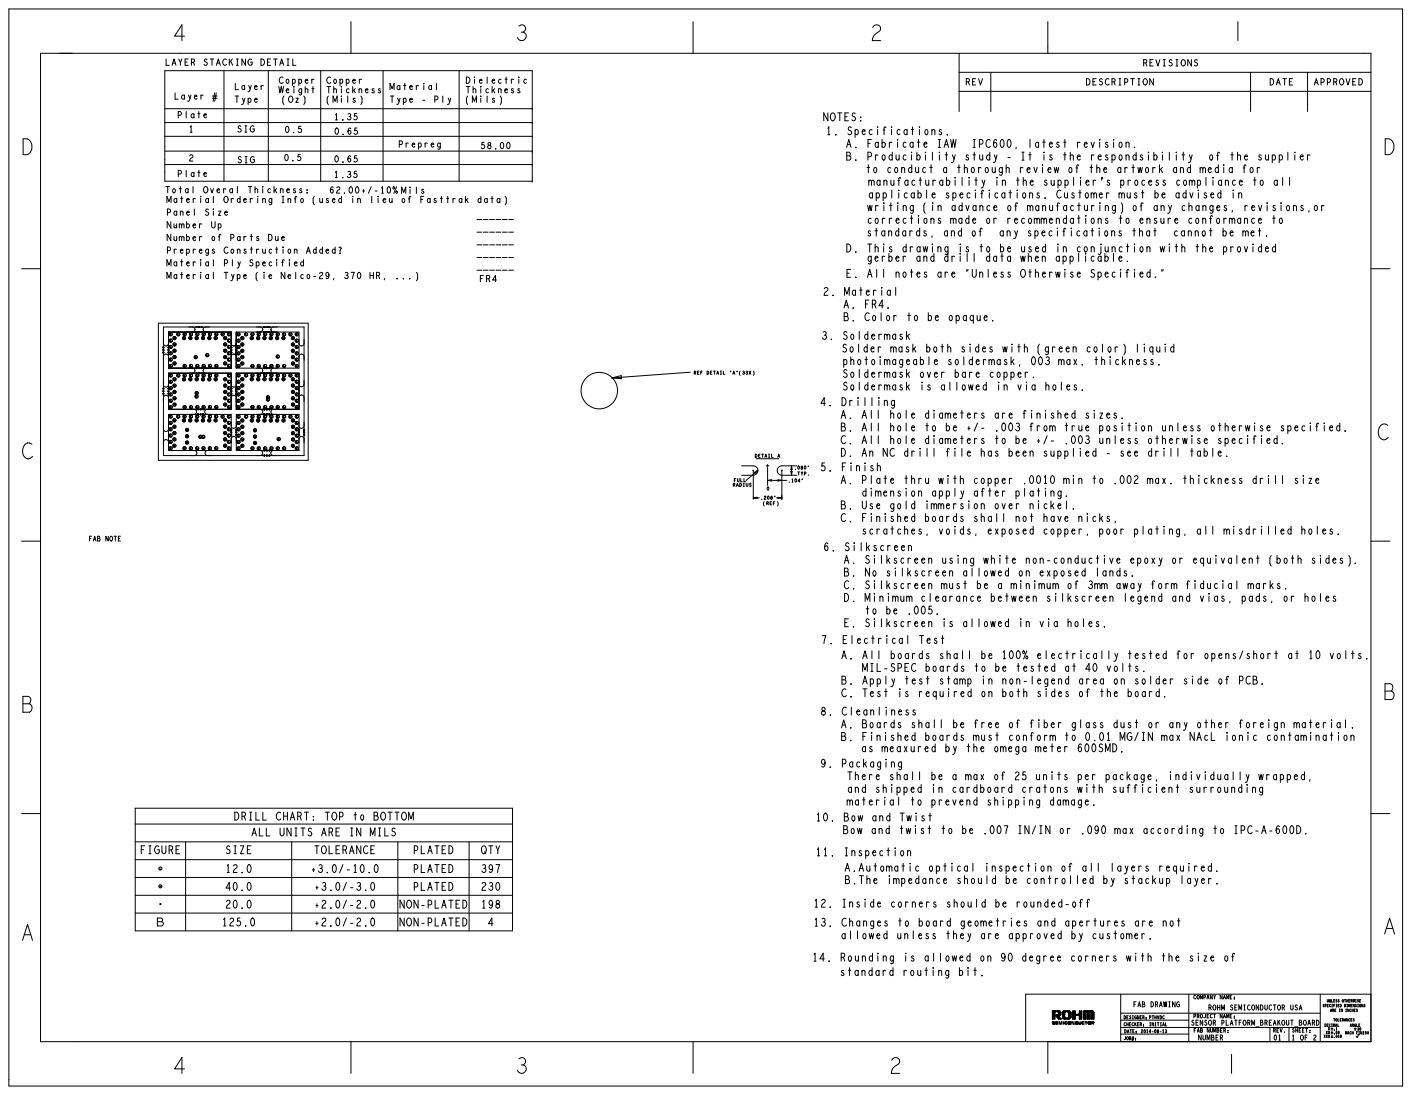
[picture p73: page 3]
